aswinkumar1999/VR_Thermal_Glove-AM5011/Images/IMG_20211215_131117.jpg

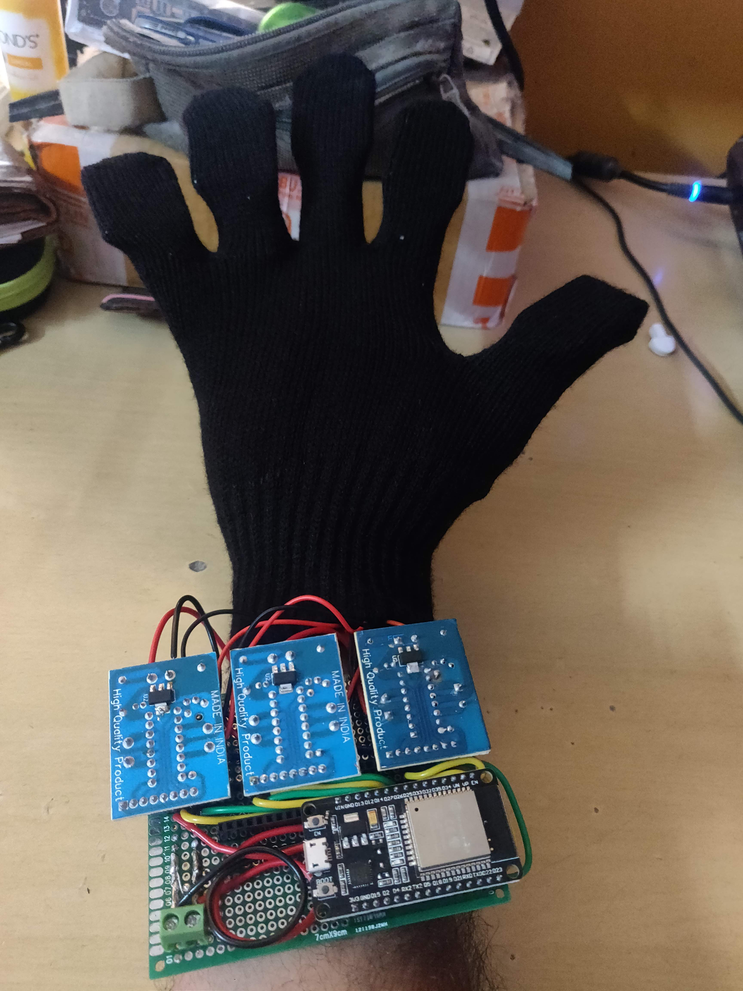
Images/IMG_20211215_131117.jpg
